petershaw/dirarare-artnet-server/hardware/Pinout-LCD.numbers/preview-web.jpg

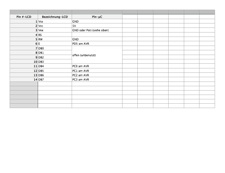
hardware/Pinout-LCD.numbers/preview-web.jpg
